sanjith1999/Analog-Piano/PCB Design/common/amplifier2.png

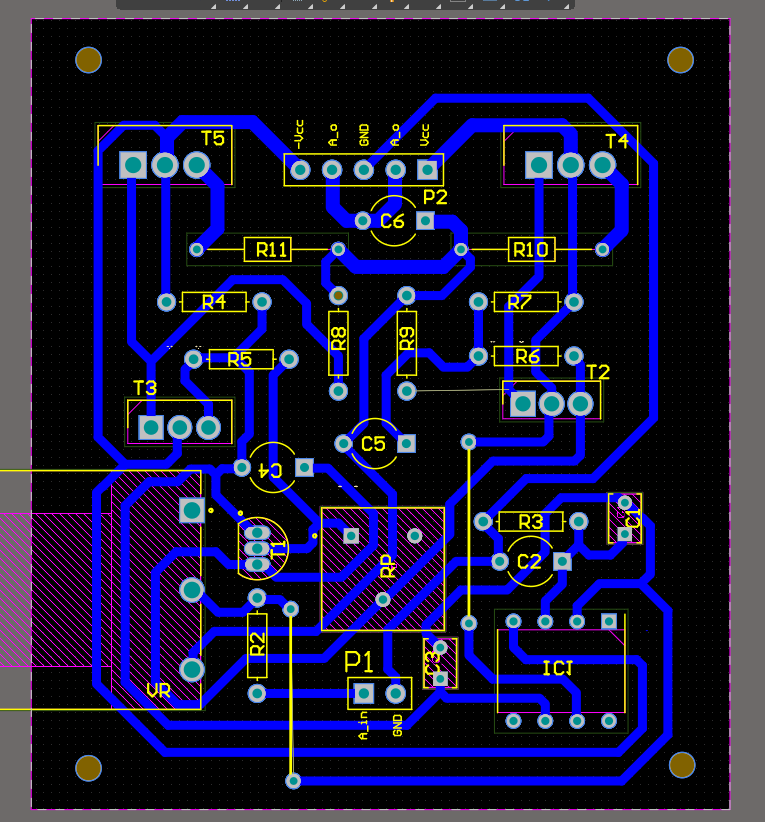
PCB Design/common/amplifier2.png
