sanjith1999/Analog-Piano/PCB Design/common/Amplifier3D.png

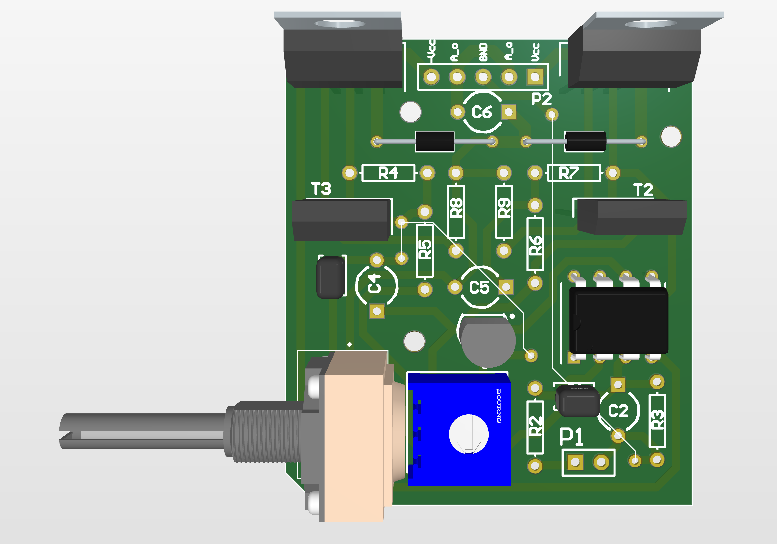
PCB Design/common/Amplifier3D.png
