sanjith1999/Analog-Piano/PCB Design/common/oscillator2D.png

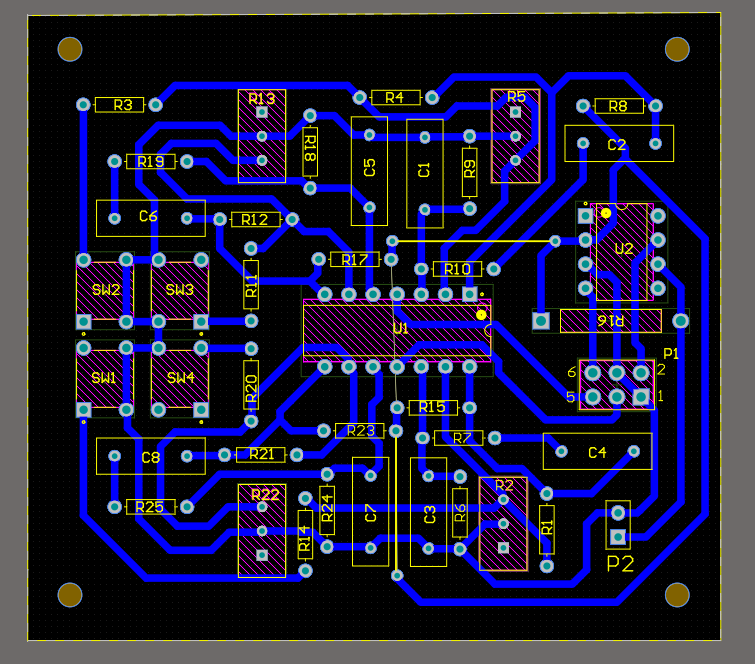
PCB Design/common/oscillator2D.png
