sanjith1999/Analog-Piano/PCB Design/common/oscillator3D.png

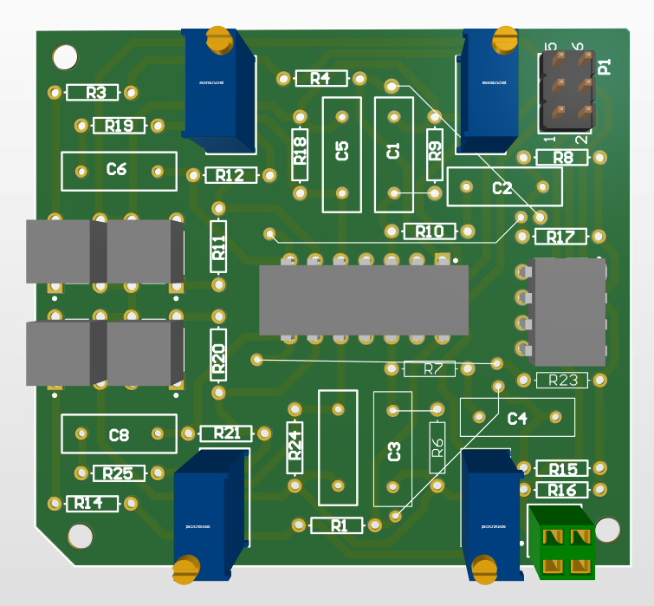
PCB Design/common/oscillator3D.png
