sanjith1999/Analog-Piano/References/ActiveFilterDesign.png

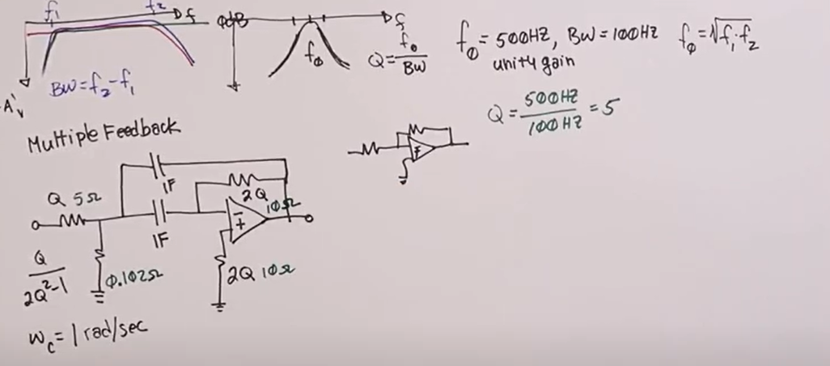
References/ActiveFilterDesign.png
