sanjith1999/Analog-Piano/Submission Files/Data Sheet/images/final_wave.jpg

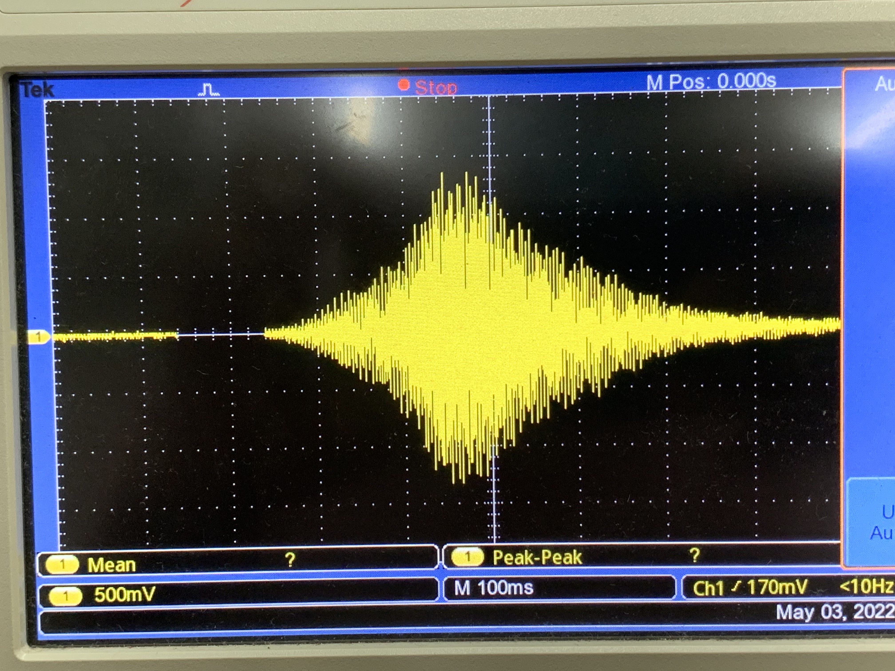
Submission Files/Data Sheet/images/final_wave.jpg
