sanjith1999/Analog-Piano/Results/blockDiagram.png

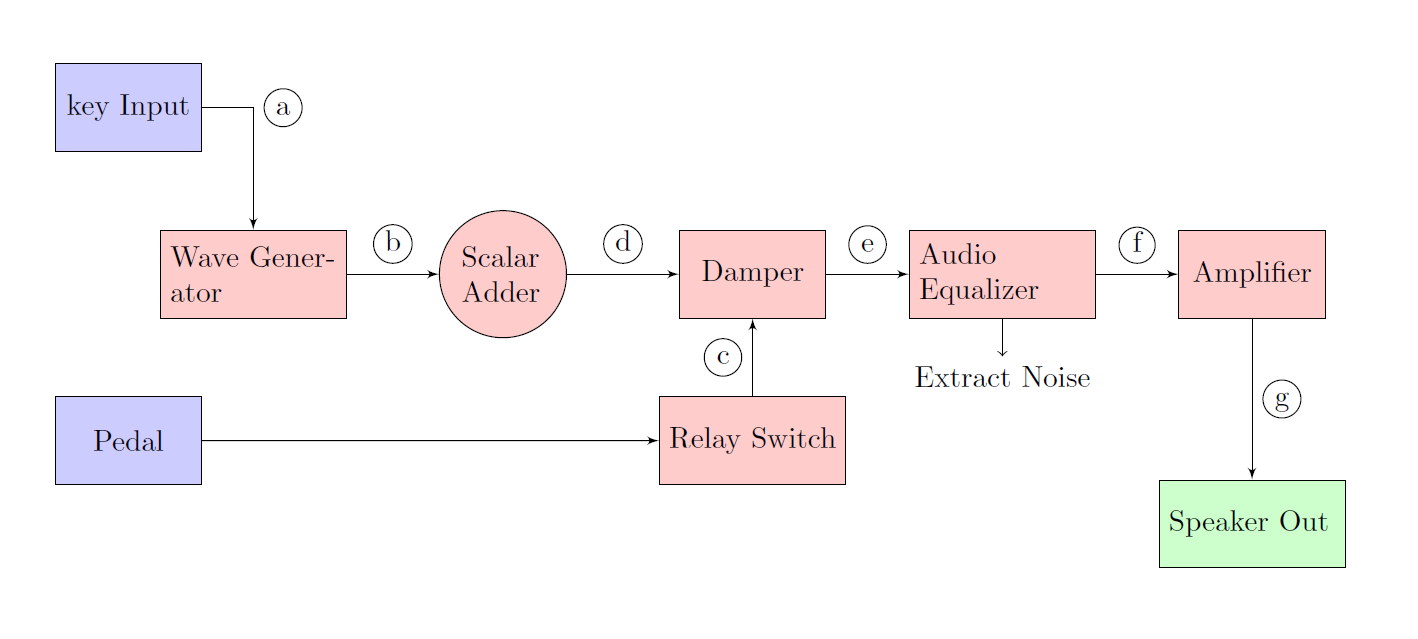
Results/blockDiagram.png
