sanjith1999/Analog-Piano/Results/circuit.jpg

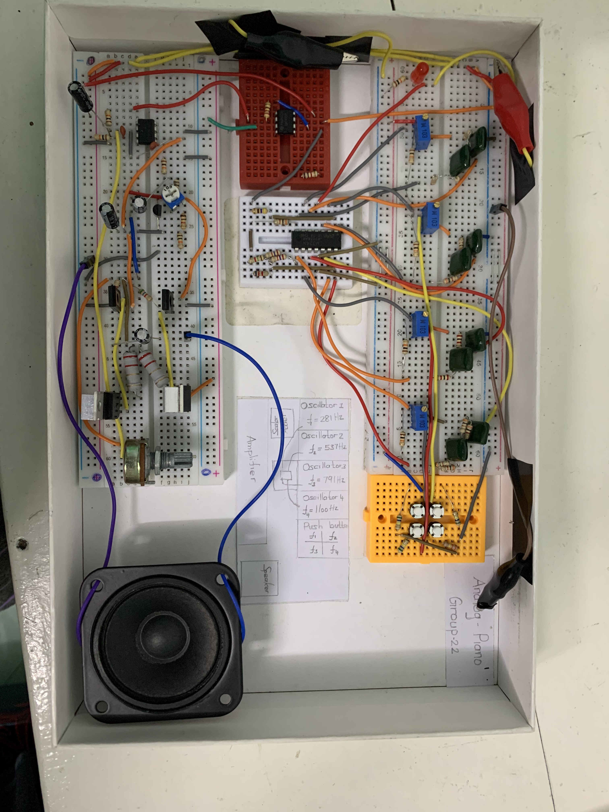
Results/circuit.jpg
