sanjith1999/Analog-Piano/Results/push-button-damping-100k.JPG

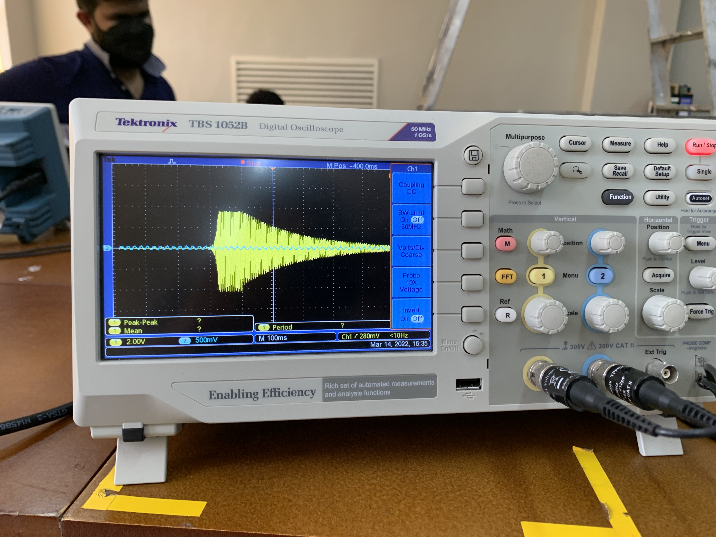
Results/push-button-damping-100k.JPG
