sanjith1999/Analog-Piano/Results/wein_phy.jpg

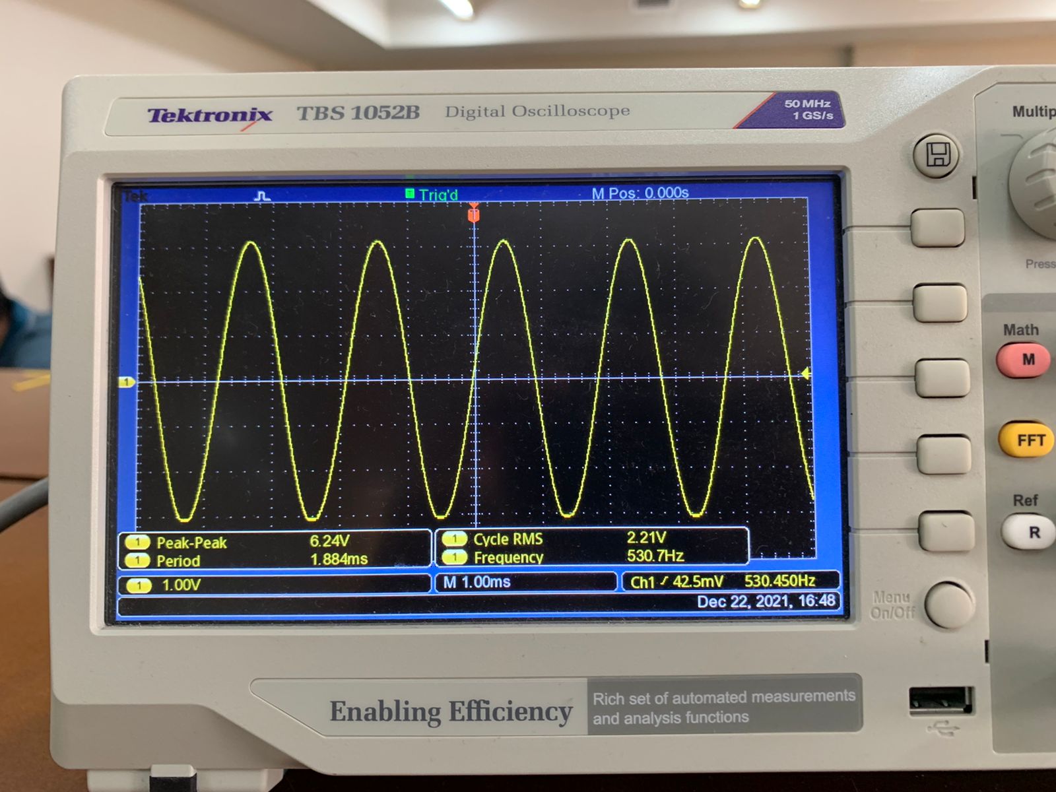
Results/wein_phy.jpg
