sanjith1999/Analog-Piano/Results/weinbridgeStimulationcirc1.jpg

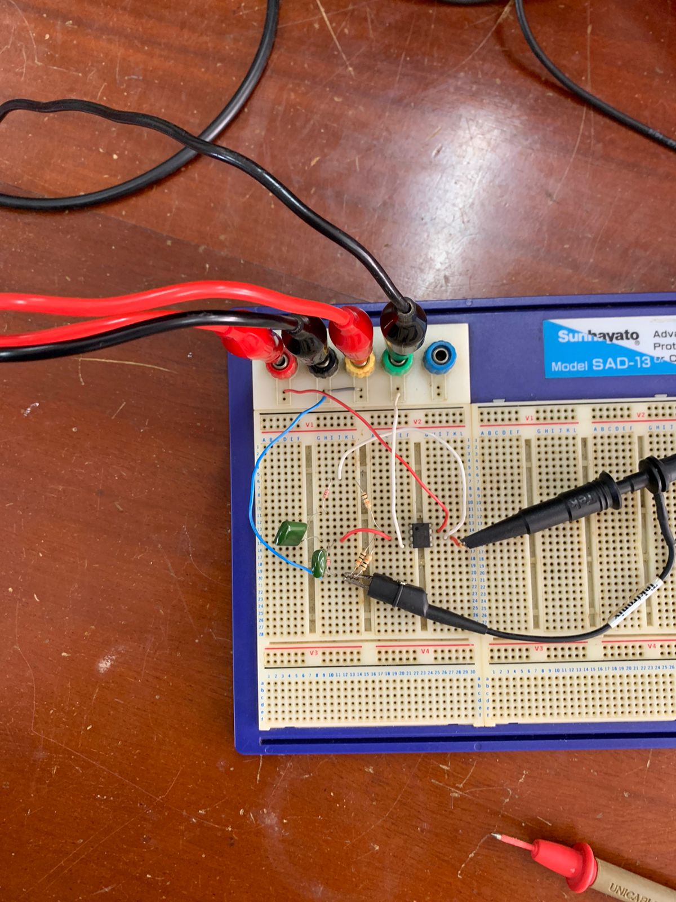
Results/weinbridgeStimulationcirc1.jpg
