sanjith1999/Analog-Piano/Results/weinbridgeStimulationcirc2.jpg

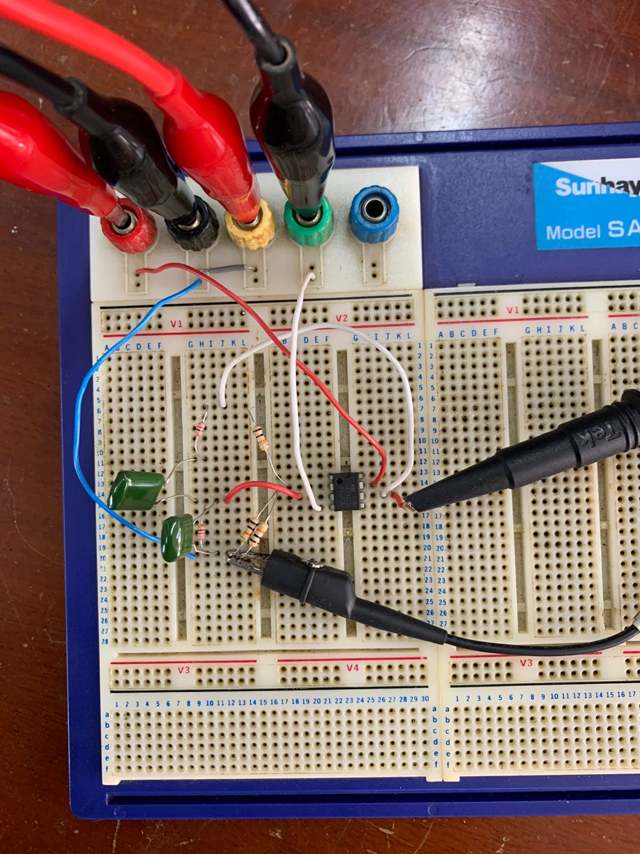
Results/weinbridgeStimulationcirc2.jpg
