sanjith1999/Analog-Piano/Results/weinbridgeStimulationsim1.jpg

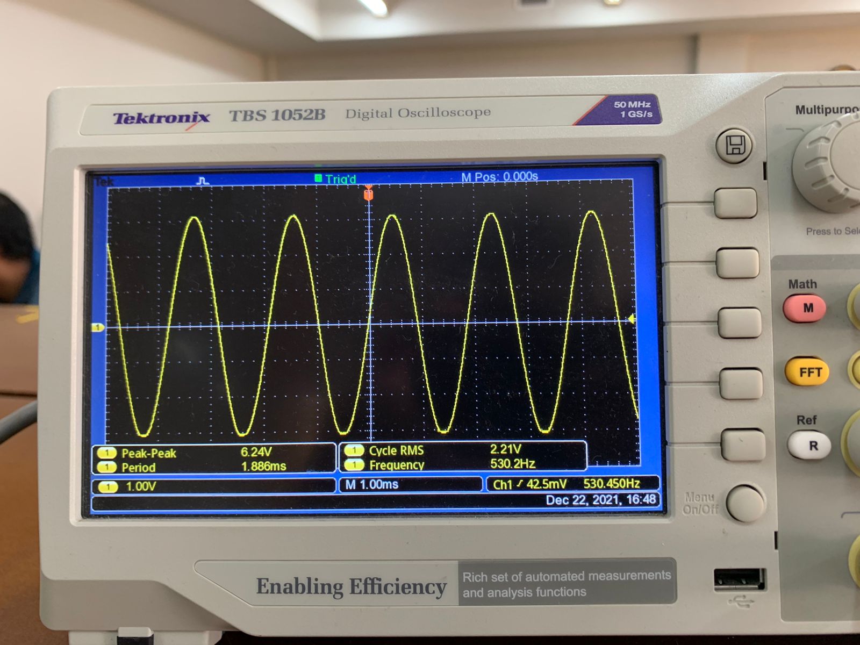
Results/weinbridgeStimulationsim1.jpg
