sanjith1999/Analog-Piano/Results/changing-parallel-resistance.JPG

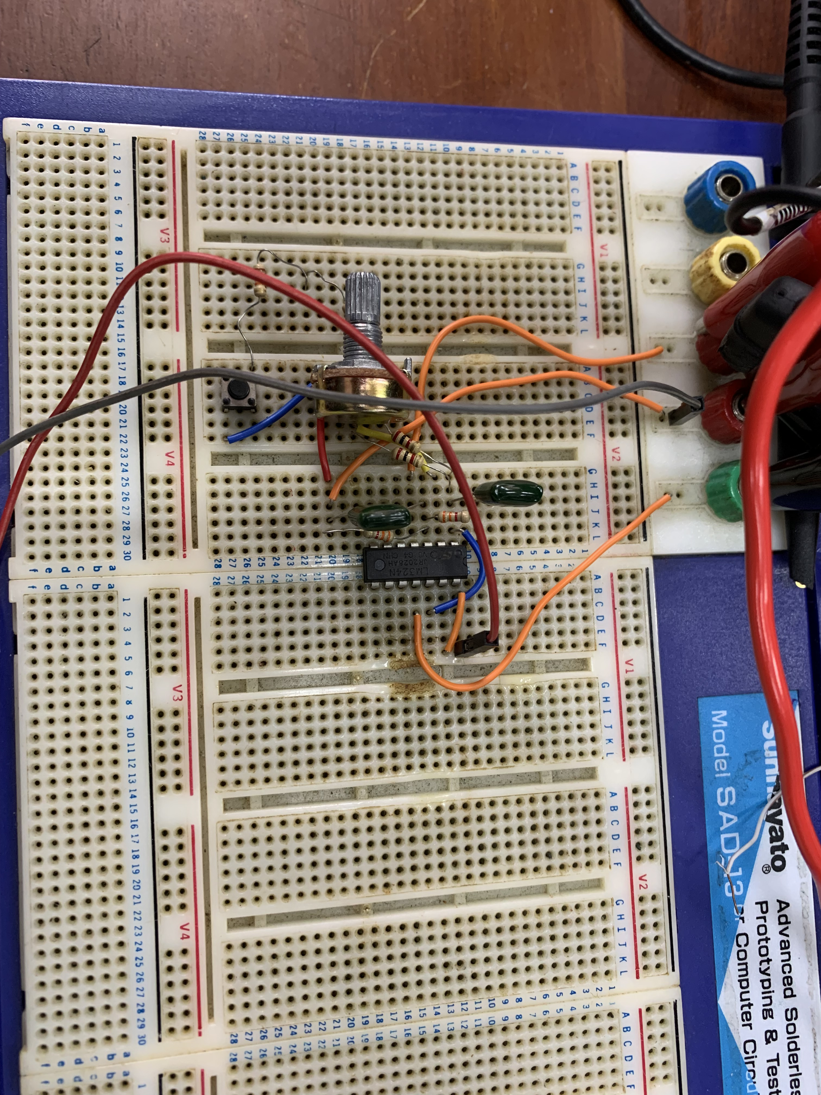
Results/changing-parallel-resistance.JPG
